didikamalova/POV-Display-RaspberryPi/media/IMG_8417.jpg

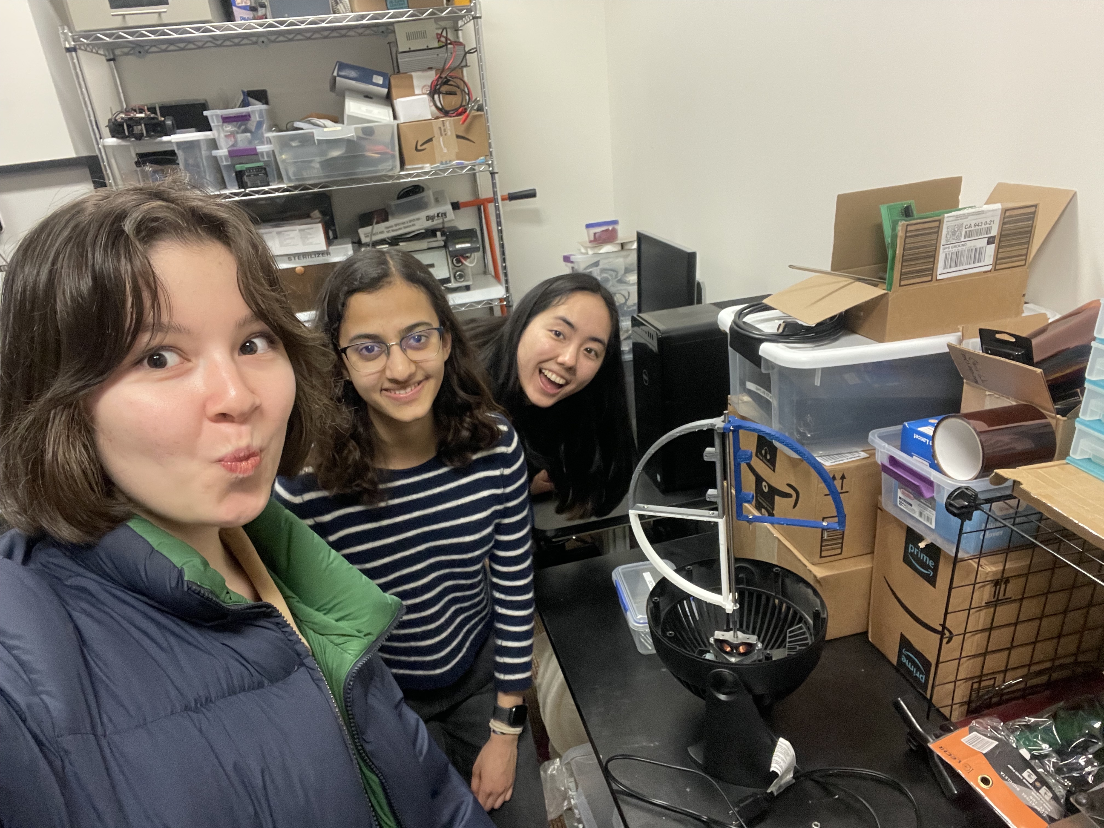
media/IMG_8417.jpg
