didikamalova/POV-Display-RaspberryPi/media/IMG_8436.jpg

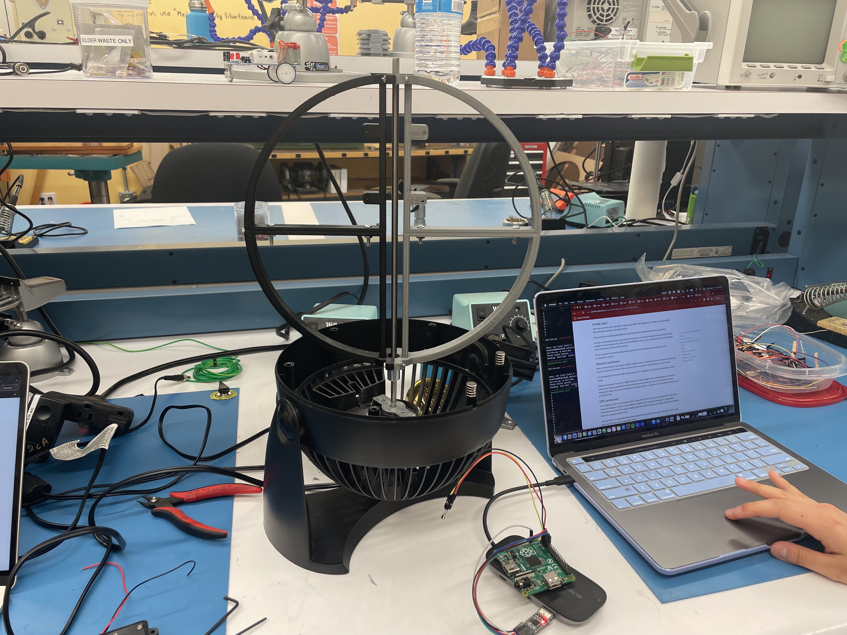
media/IMG_8436.jpg
