didikamalova/POV-Display-RaspberryPi/media/IMG_8471.jpg

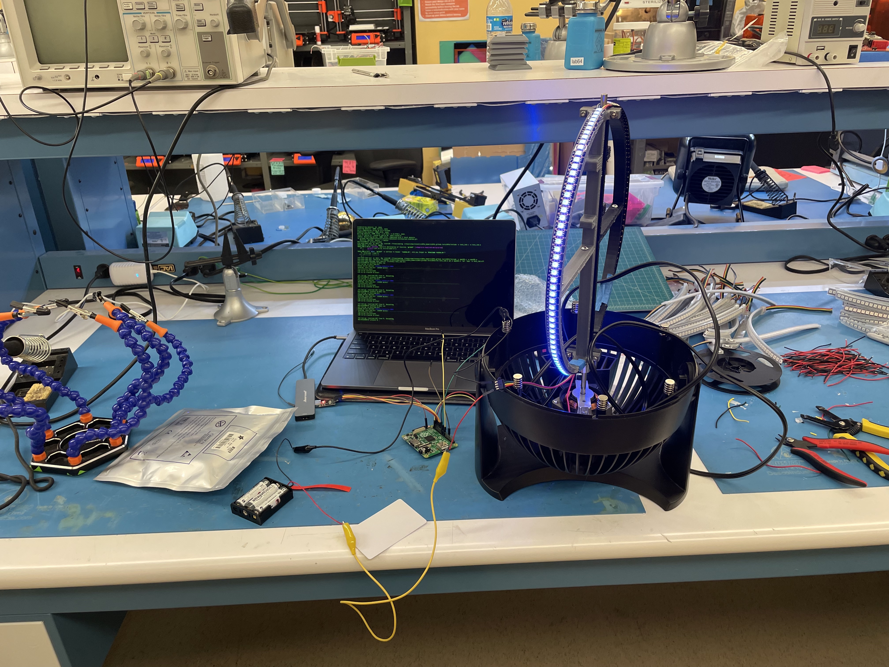
media/IMG_8471.jpg
