didikamalova/POV-Display-RaspberryPi/earth.h

/* Earth image array
 * We used this webiste for converting an image we found online to an array of the correct size (HORIZONTAL_RESOLUTION X VERTICAL_RESOLUTION).
 * Each 32bit value is in ABGR format which is the color_t format apa_102 uses.
 * Website: https://notisrac.github.io/FileToCArray/
 */

#ifndef EARTH_H
#define EARTH_H

// array size for 120x60 image so total size is 28800
const unsigned int earth_simple[]  = {
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
};

#endif
