didikamalova/POV-Display-RaspberryPi/apa102.h

#ifndef APA102_H
#define APA102_H

#include "apa102.h"

/* 
 * Number of frames the strip buffer will contain.
 * Can be smaller than than the number of LEDs 
 * physically available on the strip, but not larger.
 */

#define NUM_LEDS 120

/*
 * `color_t`
 *
 * ABGR colors, where each color component B, G, R, or A is a single 
 * unsigned byte. The least signficant byte is the R component, and A 
 * is most significant. A should always be set to 0xFF, i.e. max brightness.
 */
typedef unsigned int color_t;

/* Common Colors */
#define WHITE    0xFFFFFFFF
#define RED      0xFF0000FF
#define GREEN    0xFF00FF00
#define BLUE     0xFFFF0000

/*
 * `apa102_color`
 *
 * Returns a color composed of the specified red, green, and
 * blue components. The alpha component of the color will be
 * set to 0xff (full brightneess).
 *
 * @param r  the red component of the color
 * @param g  the green component of the color
 * @param b  the blue component of the color
 *
 * @return   the color as a single value of type color_t
 */
color_t apa102_color(unsigned char r, unsigned char g, unsigned char b);

/*
 * `apa102_init`
 *
 * Initializes the SPI connection with the Pi.
 */
void apa102_init(void);

/*
 * `apa102_clear`
 *
 * Clears all the LEDs in the buffer to the given color.
 *
 * @param c color
 */
void apa102_clear(color_t c);

/*
 * `apa102_set_led`
 *
 * Sets a single led on the buffer to a certain color.
 *
 * @param c color
 * 
 * If n is outside the bounds of the strip, does nothing.
 */
void apa102_set_led(int n, color_t c);

/*
 * `apa102_show`
 *
 * Displays the contents of the buffer on the strip.
 */
void apa102_show(void);


#endif
